aleixq/meteostation-node-term/meteostation/Meteo.cpp

/*
 Weather Shield Station
 By: Aleix Quintana Alsius
 Date: May 5th, 2018
 License: This code is public domain but you buy me a beer if you use this and we meet someday (Beerware license).

 Much of this is based on Mike Grusin's USB Weather Board code: https://www.sparkfun.com/products/10586, and later Nathan Seidle

 This code reads all the various sensors (wind speed, direction, rain gauge, humidty, pressure, light, batt_lvl)
 and reports it over the serial comm port. This can be easily routed to an datalogger (such as OpenLog) or
 a wireless transmitter (such as Electric Imp).

 Measurements are reported once a second but windspeed and rain gauge are tied to interrupts that are
 calcualted at each report.

 This example code assumes the GPS module is not used.

 */
 #include "Meteo.h"

//-=-=-=-=-=-=-=-=-=-=-=-=-=-=-=-=-=-=-=-=-=-=-=-=-=-=-=-=

//Interrupt routines (these are called by the hardware interrupts, not by the main code)
//-=-=-=-=-=-=-=-=-=-=-=-=-=-=-=-=-=-=-=-=-=-=-=-=-=-=-=-=
void rainIRQ()
// Count rain gauge bucket tips as they occur
// Activated by the magnet and reed switch in the rain gauge, attached to input D2
{
  raintime = millis(); // grab current time
  raininterval = raintime - rainlast; // calculate interval between this and last event

  if (raininterval > 10) // ignore switch-bounce glitches less than 10mS after initial edge
  {
    dailyrainin += 0.011; //Each dump is 0.011" of water
    rainHour[minutes] += 0.011; //Increase this minute's amount of rain

    rainlast = raintime; // set up for next event
  }
}

void wspeedIRQ()
// Activated by the magnet in the anemometer (2 ticks per rotation), attached to input D3 //TODO MOVED TO D4
{
  if (millis() - lastWindIRQ > 10) // Ignore switch-bounce glitches less than 10ms (142MPH max reading) after the reed switch closes
  {
    lastWindIRQ = millis(); //Grab the current time
    windClicks++; //There is 1.492MPH for each click per second.
  }
}

void blinking()
{
  digitalWrite(STAT1, HIGH);   // turn the LED on (HIGH is the voltage level)
  delay(500);              // wait for a second
  digitalWrite(STAT1, LOW);    // turn the LED off by making the voltage LOW
  delay(500);              // wait for a second
  digitalWrite(STAT1, HIGH);   // turn the LED on (HIGH is the voltage level)
  delay(500);              // wait for a second
  digitalWrite(STAT1, LOW);    // turn the LED off by making the voltage LOW
  delay(500);              // wait for a second
}


//Calculates each of the variables that wunderground is expecting
void calcWeather()
{
  //Calc winddir
  winddir = get_wind_direction();

  //Calc windspeed
  windspeedkph = get_wind_speed_kph();
  
  //Calc windgustkph
  //Calc windgustdir
  //These are calculated in the main loop

  //Calc windspdkph_avg2m
  float temp = 0;
  for(int i = 0 ; i < 120 ; i++)
    temp += windspdavg[i];
  temp /= 120.0;
  windspdkph_avg2m = temp;

  //Calc winddir_avg2m, Wind Direction
  //You can't just take the average. Google "mean of circular quantities" for more info
  //We will use the Mitsuta method because it doesn't require trig functions
  //And because it sounds cool.
  //Based on: http://abelian.org/vlf/bearings.html
  //Based on: http://stackoverflow.com/questions/1813483/averaging-angles-again
  long sum = winddiravg[0];
  int D = winddiravg[0];
  for(int i = 1 ; i < WIND_DIR_AVG_SIZE ; i++)
  {
    int delta = winddiravg[i] - D;

    if(delta < -180)
      D += delta + 360;
    else if(delta > 180)
      D += delta - 360;
    else
      D += delta;

    sum += D;
  }
  winddir_avg2m = sum / WIND_DIR_AVG_SIZE;
  if(winddir_avg2m >= 360) winddir_avg2m -= 360;
  if(winddir_avg2m < 0) winddir_avg2m += 360;

  //Calc windgustkph_10m
  //Calc windgustdir_10m
  //Find the largest windgust in the last 10 minutes
  windgustkph_10m = 0;
  windgustdir_10m = 0;
  //Step through the 10 minutes
  for(int i = 0; i < 10 ; i++)
  {
    if(windgust_10m[i] > windgustkph_10m)
    {
      windgustkph_10m = windgust_10m[i];
      windgustdir_10m = windgustdirection_10m[i];
    }
  }
  humitat = bme.readHumidity();
  temperaturac = bme.readTemperature();
  temperaturaf = temperaturac*1.8+32.0;
  dew_point = getDewPoint(temperaturac, humitat);

  barometer_raw = bme.readPressure();
  pressio = getPressureSeaLevel(city_meters_above_sea, temperaturac, bme.readPressure()/100.0F);

  //Total rainfall for the day is calculated within the interrupt
  //Calculate amount of rainfall for the last 60 minutes
  rainin = 0;
  for(int i = 0 ; i < 60 ; i++)
    rainin += rainHour[i];



  //Calc light level
  light_lvl = get_light_level();

  //Calc battery level
  batt_lvl = get_battery_level();
}

//Returns the voltage of the light sensor based on the 3.3V rail
//This allows us to ignore what VCC might be (an Arduino plugged into USB has VCC of 4.5 to 5.2V)
float get_light_level()
{
  float operatingVoltage = analogRead(REFERENCE_3V3);

  float lightSensor = analogRead(LIGHT);

  operatingVoltage = 3.3 / operatingVoltage; //The reference voltage is 3.3V

  lightSensor = operatingVoltage * lightSensor;

  return(lightSensor);
}

//Returns the voltage of the raw pin based on the 3.3V rail
//This allows us to ignore what VCC might be (an Arduino plugged into USB has VCC of 4.5 to 5.2V)
//Battery level is connected to the RAW pin on Arduino and is fed through two 5% resistors:
//3.9K on the high side (R1), and 1K on the low side (R2)
float get_battery_level()
{
  float operatingVoltage = analogRead(REFERENCE_3V3);

  float rawVoltage = analogRead(BATT);

  operatingVoltage = 3.30 / operatingVoltage; //The reference voltage is 3.3V

  rawVoltage = operatingVoltage * rawVoltage; //Convert the 0 to 1023 int to actual voltage on BATT pin

  rawVoltage *= 4.90; //(3.9k+1k)/1k - multiple BATT voltage by the voltage divider to get actual system voltage

  return(rawVoltage);
}

//Returns the instataneous wind speed
float get_wind_speed()
{
  float deltaTime = millis() - lastWindCheck; //750ms

  deltaTime /= 1000.0; //Covert to seconds

  float windSpeed = (float)windClicks / deltaTime; //3 / 0.750s = 4

  windClicks = 0; //Reset and start watching for new wind
  lastWindCheck = millis();

  windSpeed *= 1.492; //4 * 1.492 = 5.968MPH

  return(windSpeed);
}

//Returns the instataneous wind speed
float get_wind_speed_ms()
{
  float deltaTime = millis() - lastWindCheck; //750ms

  deltaTime /= 1000.0; //Covert to seconds

  if((float)windClicks == 0.00){
    return(0.0);
  }
  float windSpeed = (float)windClicks / deltaTime; //3 / 0.750s = 4

  windClicks = 0; //Reset and start watching for new wind
  lastWindCheck = millis();

  windSpeed *= 0.66; //4 * 0.66 = 2.64ms

  return(windSpeed);
}

//Returns the instataneous wind speed in kph
float get_wind_speed_kph()
{
  float deltaTime = millis() - lastWindCheck; //750ms
  deltaTime /= 1000.0; //Convert to hours

  if((float)windClicks == 0.00){
    return(0.0);
  }
  float windSpeed = (float)windClicks / deltaTime; // 3 / 0.750s = 4
  
  windClicks = 0; //Reset and start watching for new wind
  lastWindCheck = millis();

  windSpeed *= 2.4; //4 * 0.66 = 2.64ms

  return(windSpeed);
}


//Read the wind direction sensor, return heading in degrees
int get_wind_direction()
{
  unsigned int adc;

  adc = analogRead(WDIR); // get the current reading from the sensor

  // The following table is ADC readings for the wind direction sensor output, sorted from low to high.
  // Each threshold is the midpoint between adjacent headings. The output is degrees for that ADC reading.
  // Note that these are not in compass degree order! See Weather Meters datasheet for more information.

  if (adc < 380) return (113);
  if (adc < 393) return (68);
  if (adc < 414) return (90);
  if (adc < 456) return (158);
  if (adc < 508) return (135);
  if (adc < 551) return (203);
  if (adc < 615) return (180);
  if (adc < 680) return (23);
  if (adc < 746) return (45);
  if (adc < 801) return (248);
  if (adc < 833) return (225);
  if (adc < 878) return (338);
  if (adc < 913) return (0);
  if (adc < 940) return (293);
  if (adc < 967) return (315);
  if (adc < 990) return (270);
  return (-1); // error, disconnected?
}

/****************************************************************/
/** From https://github.com/finitespace/BME280 **/
float getPressureSeaLevel
(
  float altitude,
  float temp,
  float pres
)
{
    float seaPress = NAN;
    if(!isnan(altitude) && !isnan(temp) && !isnan(pres))
    {
        seaPress = (pres / pow(1 - ((0.0065 *altitude) / (temp + (0.0065 *altitude) + 273.15)), 5.257));
    }
    return seaPress;
}

/****************************************************************/
float getDewPoint
(
  float temp,
  float hum
)
{
  // Equations courtesy of Brian McNoldy from http://andrew.rsmas.miami.edu;
  float dewPoint = NAN;

  if(!isnan(temp) && !isnan(hum))
  {
     dewPoint = 243.04 * (log(hum/100.0) + ((17.625 * temp)/(243.04 + temp)))
       /(17.625 - log(hum/100.0) - ((17.625 * temp)/(243.04 + temp)));
  }

  return dewPoint;
}
